mean00/powersupply_arduinopowered/power_screen.h

#include "U8g2lib.h"
/**
 * 
 */
class powerSupplyScreen
{
public:
        powerSupplyScreen() ;  
  void  printStatus(int line,const char *s);
  void  setVoltage(unsigned int voltage) ;
  void  setCurrent(int mA,int maxA,bool connected) ;
  void  setCurrentCalibration(int mA,int rawReading,bool limited) ;
  void  setLimitOn(bool limit);
  void  refresh();

protected:
    U8G2_PCD8544_84X48_1_4W_HW_SPI u8g;
    char           stV[20]; // voltage
    char           stA[20]; // current
    char           stM[20]; // max current
    bool           displayLimit; // true if current limiting is on

};
