mean00/powersupply_arduinopowered/wav_rotary.h

#pragma once
/**
 */
enum WavDirection
{
  WavNone=0,
  WavLeft,
  WavRight
};
/**
 */
class WavRotary
{
public:
                     WavRotary(int pinA,int pinB );
        WavDirection getSense();
protected:
        Rotary       _rotary;
};
